jromanki/fpga-fm-synth/hardware/fpga-fm-synth-kicad/fpga-fm-synth-kicad.kicad_sch

## KiCad design hardware/fpga-fm-synth-kicad/fpga-fm-synth-kicad.kicad_sch (2026-05-16, an earlier design)

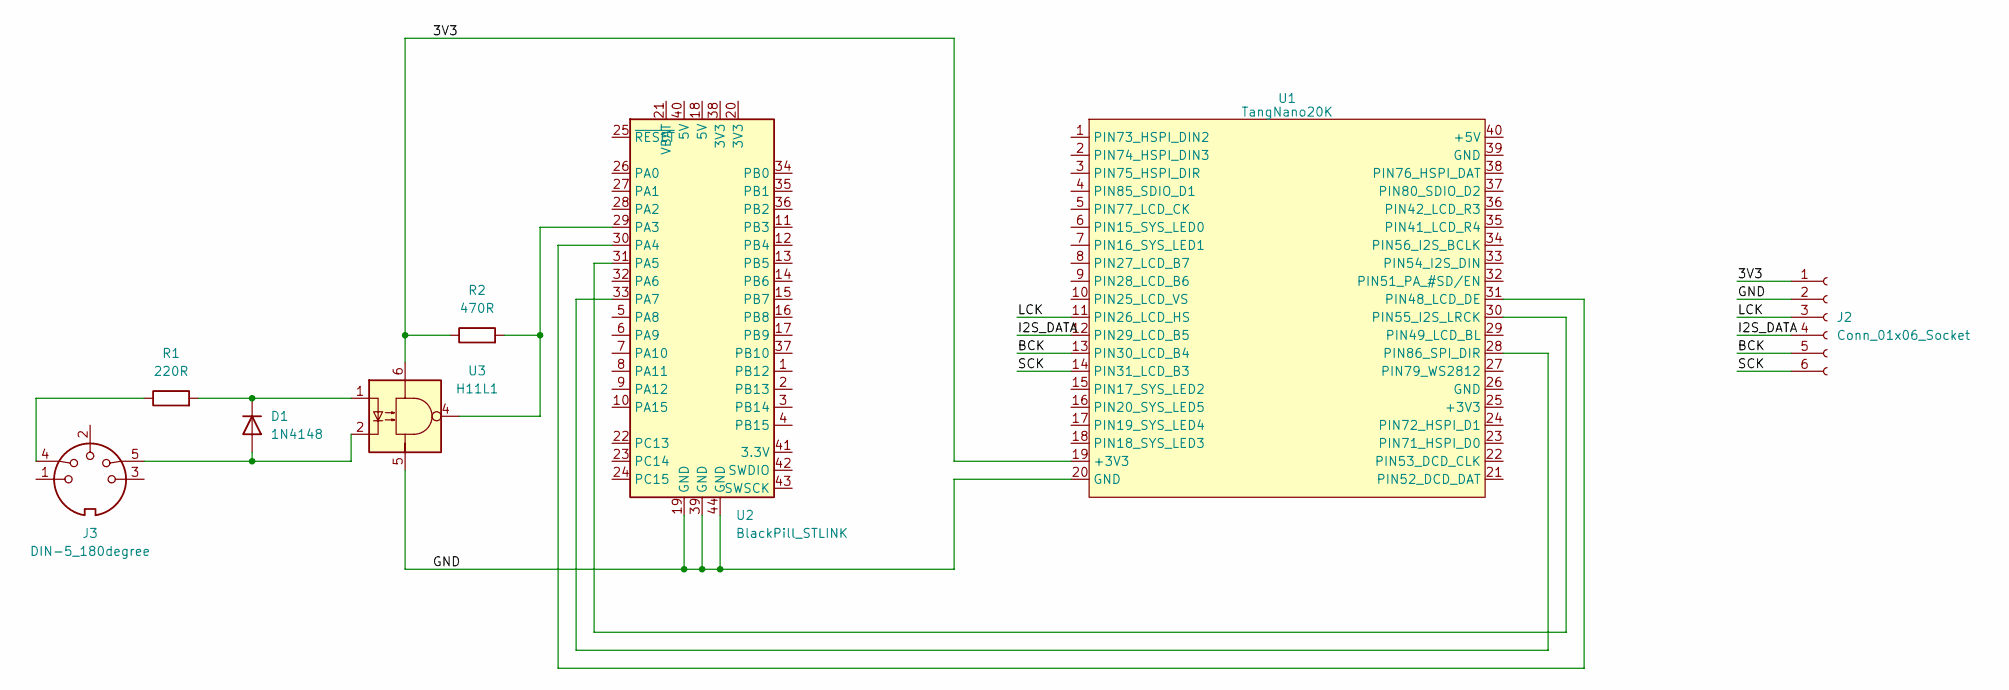
[picture p2: schematic fpga-fm-synth-kicad.kicad_sch]

Parts:
D1: 1N4148; D_DO-35_SOD27_P7.62mm_Horizontal
J2: Conn_01x06_Socket
J3: DIN-5_180degree
R1: 220R
R2: 470R
U1: TangNano20K
U2: BlackPill_STLINK
U3: H11L1

Connections:
3V3: J2.1, R2.1, U1.19 (+3V3), U3.6
BCK: J2.5, U1.13 (PIN30_LCD_B4)
GND: J2.2, U1.20 (GND), U2.19 (GND), U2.39 (GND), U2.44 (GND), U3.5
I2S_DATA: J2.4, U1.12 (PIN29_LCD_B5)
LCK: J2.3, U1.11 (PIN26_LCD_HS)
unnamed: D1.1 (K), R1.2, U3.1
unnamed: D1.2 (A), J3.5, U3.2
unnamed: J3.4, R1.1
unnamed: R2.2, U2.29 (PA3), U3.4
unnamed: U1.28 (PIN86_SPI_DIR), U2.33 (PA7)
unnamed: U1.30 (PIN55_I2S_LRCK), U2.31 (PA5)
unnamed: U1.31 (PIN48_LCD_DE), U2.30 (PA4)
SCK: J2.6, U1.14 (PIN31_LCD_B3)
