jromanki/fpga-fm-synth/control-blackpill/Core/Src/usart.c

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
/* Includes ------------------------------------------------------------------*/
#include "usart.h"

/* USER CODE BEGIN 0 */
#include "cmsis_os2.h"

extern uint8_t rx_buffer;
extern osMessageQueueId_t midi_queueHandle;
/* USER CODE END 0 */

UART_HandleTypeDef huart2;

/* USART2 init function */

void MX_USART2_UART_Init(void)
{

  huart2.Instance = USART2;
  huart2.Init.BaudRate = 31250;
  huart2.Init.WordLength = UART_WORDLENGTH_8B;
  huart2.Init.StopBits = UART_STOPBITS_1;
  huart2.Init.Parity = UART_PARITY_NONE;
  huart2.Init.Mode = UART_MODE_RX;
  huart2.Init.HwFlowCtl = UART_HWCONTROL_NONE;
  huart2.Init.OverSampling = UART_OVERSAMPLING_16;
  if (HAL_UART_Init(&huart2) != HAL_OK)
  {
    Error_Handler();
  }
}

void HAL_UART_MspInit(UART_HandleTypeDef* uartHandle)
{

  GPIO_InitTypeDef GPIO_InitStruct = {0};
  if(uartHandle->Instance==USART2)
  {
    /* USART2 clock enable */
    __HAL_RCC_USART2_CLK_ENABLE();

    __HAL_RCC_GPIOA_CLK_ENABLE();
    /**USART2 GPIO Configuration
    PA2     ------> USART2_TX
    PA3     ------> USART2_RX
    */
    GPIO_InitStruct.Pin = GPIO_PIN_2|GPIO_PIN_3;
    GPIO_InitStruct.Mode = GPIO_MODE_AF_PP;
    GPIO_InitStruct.Pull = GPIO_NOPULL;
    GPIO_InitStruct.Speed = GPIO_SPEED_FREQ_VERY_HIGH;
    GPIO_InitStruct.Alternate = GPIO_AF7_USART2;
    HAL_GPIO_Init(GPIOA, &GPIO_InitStruct);

    /* USART2 interrupt Init */
    HAL_NVIC_SetPriority(USART2_IRQn, 5, 0);
    HAL_NVIC_EnableIRQ(USART2_IRQn);
  }
}

void HAL_UART_MspDeInit(UART_HandleTypeDef* uartHandle)
{

  if(uartHandle->Instance==USART2)
  {
    /* Peripheral clock disable */
    __HAL_RCC_USART2_CLK_DISABLE();

    /**USART2 GPIO Configuration
    PA2     ------> USART2_TX
    PA3     ------> USART2_RX
    */
    HAL_GPIO_DeInit(GPIOA, GPIO_PIN_2|GPIO_PIN_3);

    /* USART2 interrupt Deinit */
    HAL_NVIC_DisableIRQ(USART2_IRQn);
  }
}

/* USER CODE BEGIN 1 */
void HAL_UART_RxCpltCallback(UART_HandleTypeDef *huart)
{
    uint8_t msg = rx_buffer;
    if (msg != 0xFE){
      // HAL_GPIO_TogglePin(GPIOC, GPIO_PIN_13);
      osMessageQueuePut(midi_queueHandle, &msg, 0, 0);
    }
    HAL_UART_Receive_IT(&huart2, &rx_buffer, 1);
}
/* USER CODE END 1 */
