jromanki/fpga-fm-synth/control-blackpill/Core/Inc/midi.h

#ifndef __MIDI_H__
#define __MIDI_H__

#include <stdint.h>

#define NUM_OF_VOICES                       10
#define NUM_OF_FREQ_MULT_OPTIONS            7

#define STATUS_BIT_MASK                     0x80
#define STATUS_BIT_POS                      7

/* FOR STATUS_BYTES*/
#define MSG_KIND_BIT_MASK                   0x70
#define MSG_KIND_BIT_POS                    4
#define CHANNEL_BIT_MASK                    0x0F

#define NOTE_OFF_MSG                        0
#define NOTE_ON_MSG                         1
#define POLY_AFT_MSG                        2
#define CTRL_CHG_MSG                        3
#define PROG_CHG_MSG                        4
#define CHAN_AFT_MSG                        5
#define PITCH_BND_MSG                       6
#define SYS_MSG                             7

#define CC_MOD_DEPTH                        1
#define CC_CHAN_VOLUME                      7
#define CC_MOD_FREQ_MULT                    70

/* FOR DATA BYTES */
#define DATA_BIT_MASK                       0x7F

#define MY_CHANNEL                          0

#define HAS_STATUS_BIT(byte) ((byte & STATUS_BIT_MASK) != 0)

typedef struct {
  uint32_t data;
  uint8_t target_osc;
  uint8_t msg_type;
} fpga_msg_t;

void process_midi(uint8_t rcv_msg);
void display_freq_mult(uint8_t freq_mult);

#endif
