jromanki/fpga-fm-synth/control-blackpill/freertos-blink.ioc

Mcu.UserName=STM32F411CEUx
PA13.Signal=SYS_JTMS-SWDIO
PA14.Signal=SYS_JTCK-SWCLK
PA2.Signal=USART2_TX
PA3.Signal=USART2_RX
PA4.Signal=GPIO_Output
PA5.Signal=SPI1_SCK
PA6.Signal=SPI1_MISO
PA7.Signal=SPI1_MOSI
PB1.Signal=GPIO_Output
PB10.Signal=GPIO_Output
PB2.Signal=GPIO_Output
PC13-ANTI_TAMP.Signal=GPIO_Output
